Projeto-Guarda-Rios/PCB/Resources/AquaNode_v2_image_bottom.png

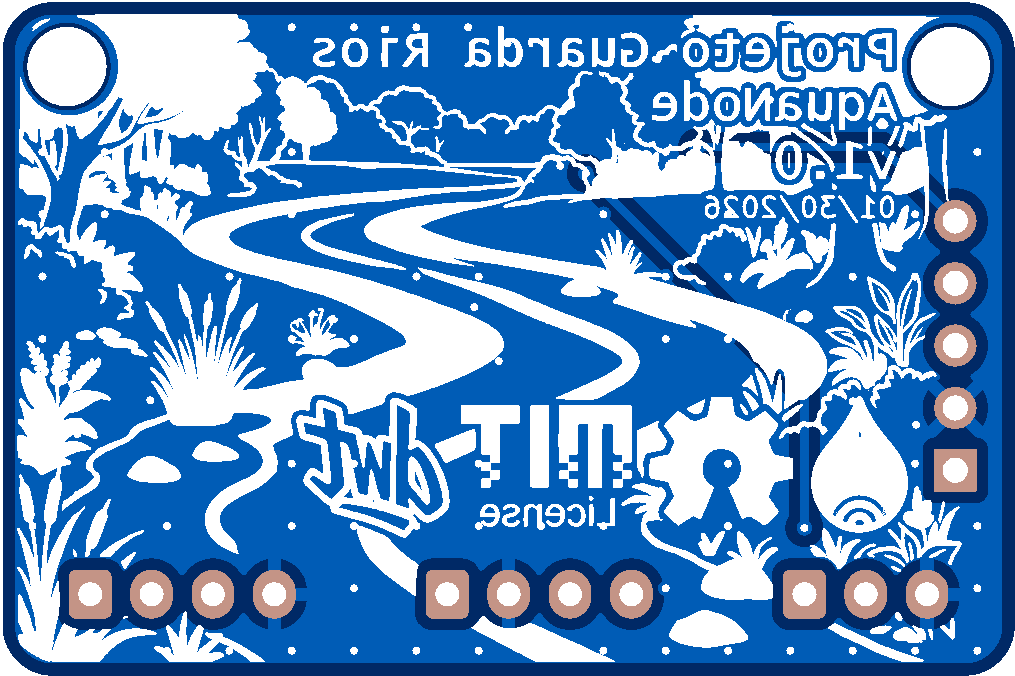
Resources/AquaNode_v2_image_bottom.png
