Projeto-Guarda-Rios/PCB/Resources/PGR_v5.1_image_bottom.png

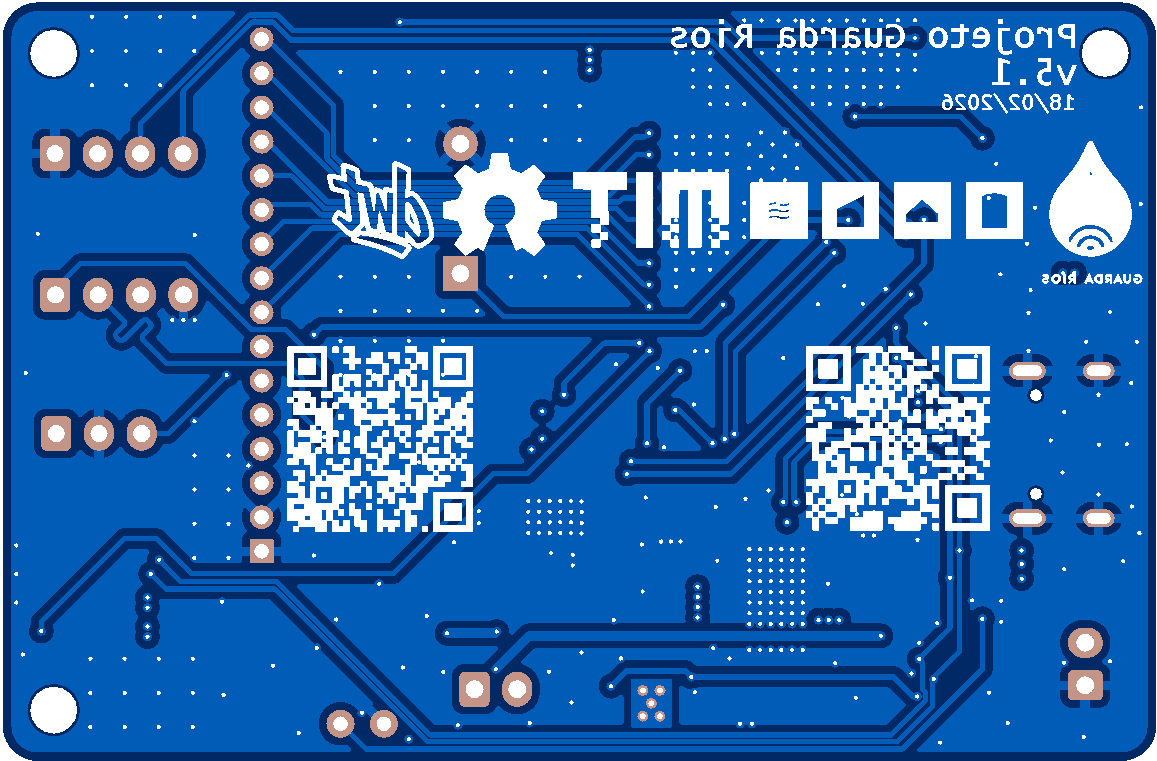
Resources/PGR_v5.1_image_bottom.png
