Projeto-Guarda-Rios/PCB/Resources/PGR_v5.1_image_top.png

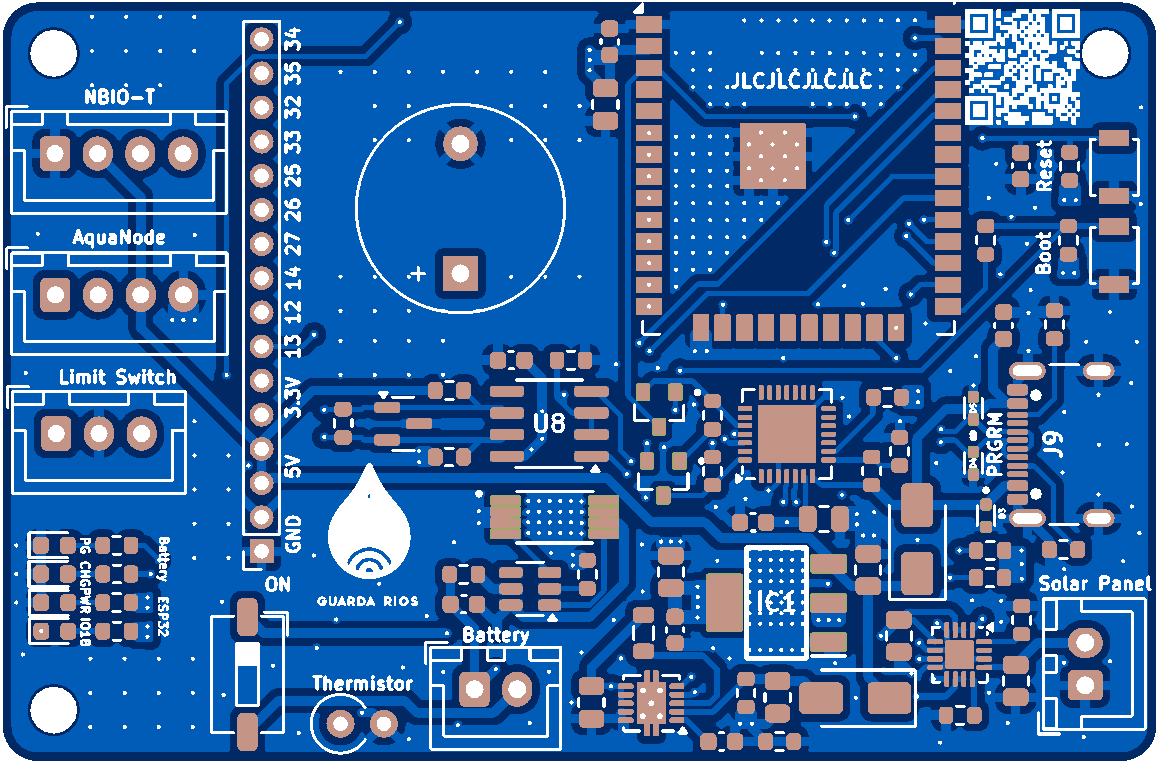
Resources/PGR_v5.1_image_top.png
